pavannaik2004/Beekeeping-DTL/06-digital-twin/exports/step/super_wall_right.step

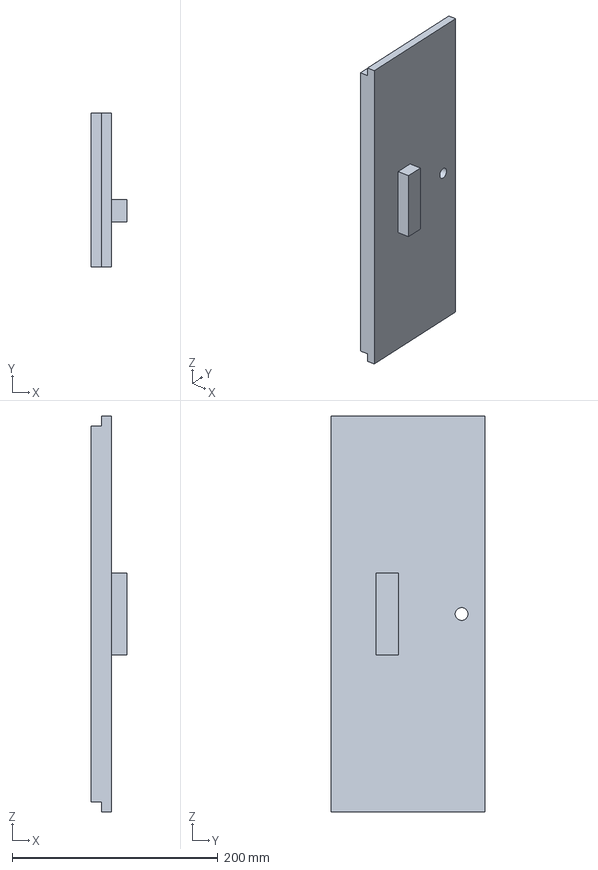
[picture p82: CAD file, 2026-07-14]
06-digital-twin/exports/step/super_wall_right.step
35.0 x 150.0 x 384.6 mm
