pavannaik2004/Beekeeping-DTL/06-digital-twin/exports/step/collection_jar.step

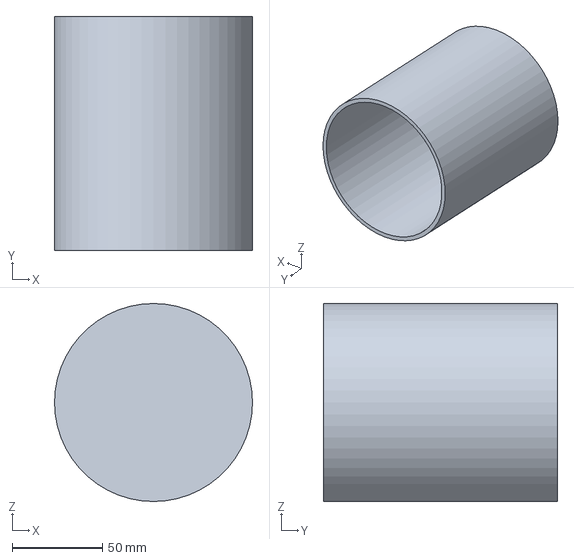
[picture p84: CAD file, 2026-07-14]
06-digital-twin/exports/step/collection_jar.step
110.0 x 130.0 x 110.0 mm
