pavannaik2004/Beekeeping-DTL/06-digital-twin/exports/step/acrylic_left.step

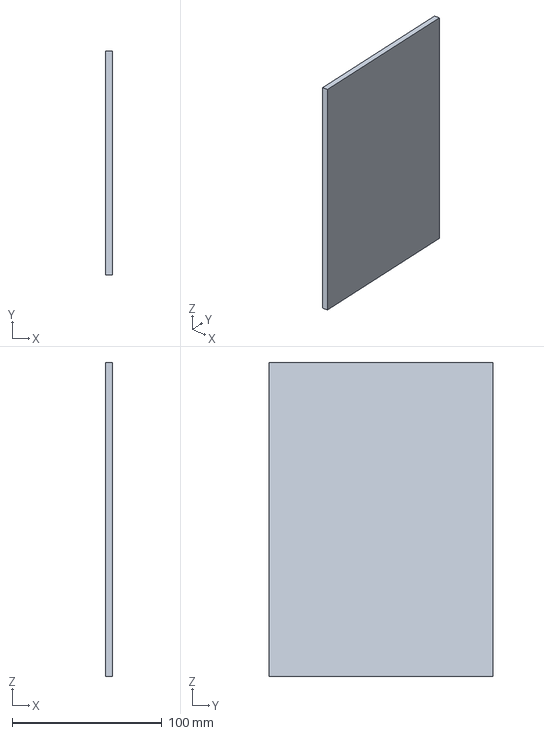
[picture p85: CAD file, 2026-07-14]
06-digital-twin/exports/step/acrylic_left.step
5.00 x 149.8 x 209.8 mm
