pavannaik2004/Beekeeping-DTL/06-digital-twin/exports/step/ff3_fixed.step

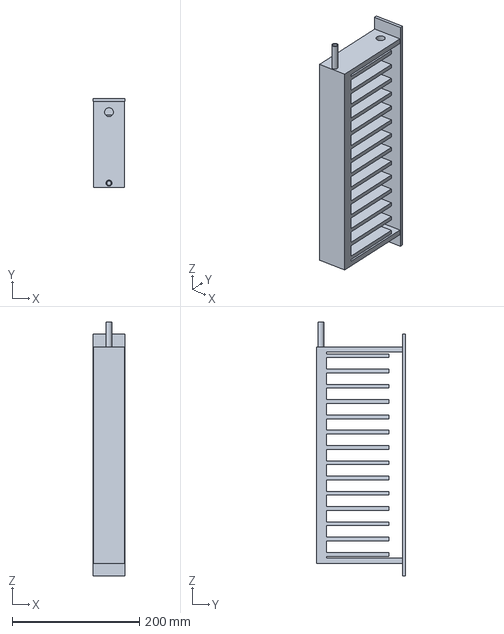
[picture p86: CAD file, 2026-07-14]
06-digital-twin/exports/step/ff3_fixed.step
49.8 x 140.0 x 399.0 mm
