pavannaik2004/Beekeeping-DTL/06-digital-twin/exports/step/acrylic_back.step

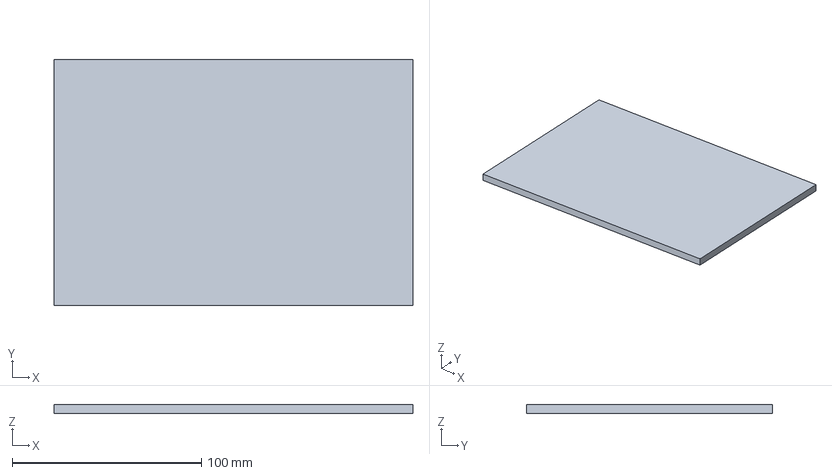
[picture p87: CAD file, 2026-07-14]
06-digital-twin/exports/step/acrylic_back.step
189.8 x 129.8 x 5.00 mm
