pavannaik2004/Beekeeping-DTL/06-digital-twin/exports/step/inner_cover.step

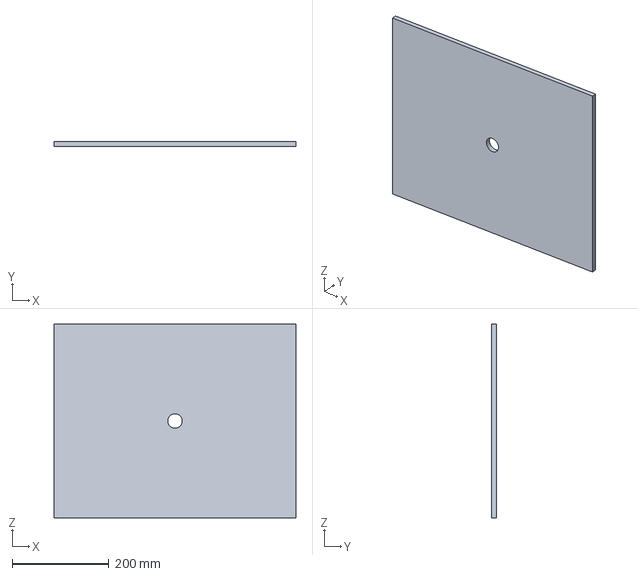
[picture p88: CAD file, 2026-07-14]
06-digital-twin/exports/step/inner_cover.step
501.0 x 10.0 x 401.0 mm
