pavannaik2004/Beekeeping-DTL/06-digital-twin/exports/step/insulation_back.step

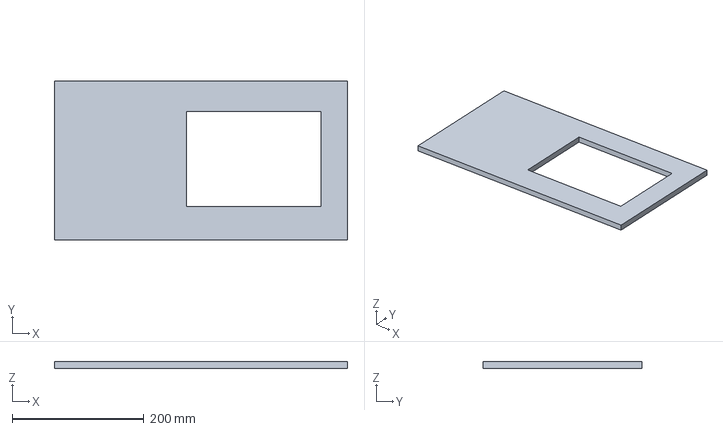
[picture p89: CAD file, 2026-07-14]
06-digital-twin/exports/step/insulation_back.step
445.0 x 241.0 x 10.0 mm
