pavannaik2004/Beekeeping-DTL/06-digital-twin/exports/step/manifold.step

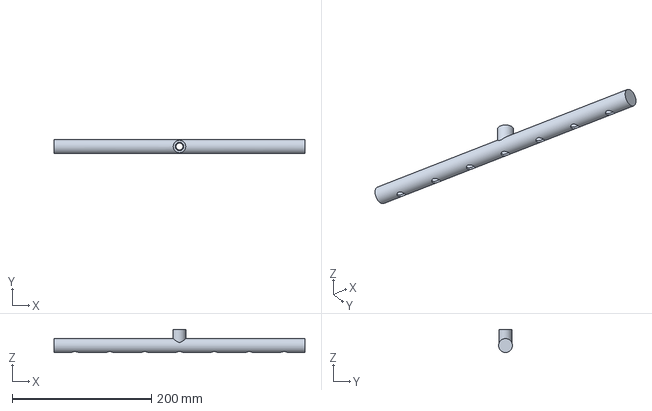
[picture p90: CAD file, 2026-07-14]
06-digital-twin/exports/step/manifold.step
360.0 x 20.0 x 33.0 mm
