pavannaik2004/Beekeeping-DTL/06-digital-twin/exports/step/feeder_tray.step

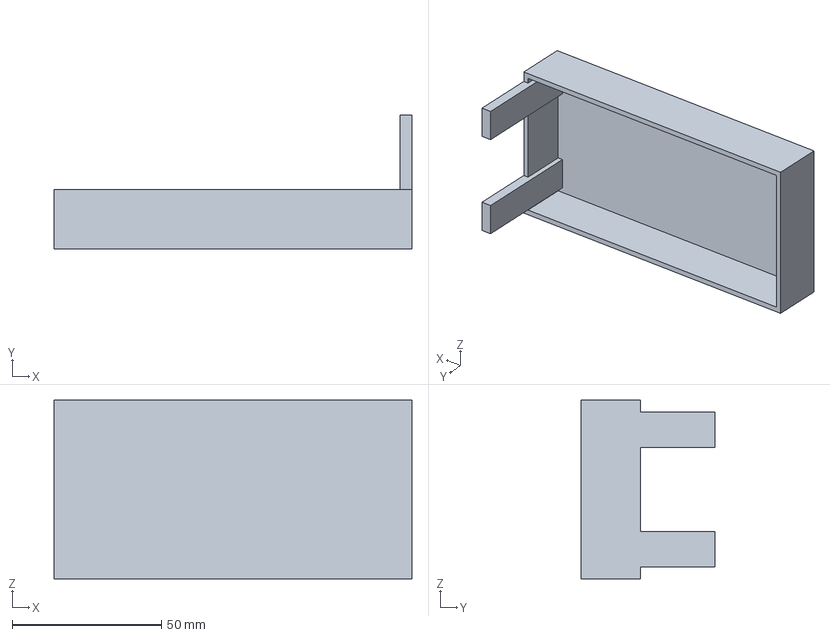
[picture p91: CAD file, 2026-07-14]
06-digital-twin/exports/step/feeder_tray.step
120.0 x 45.0 x 60.0 mm
