pavannaik2004/Beekeeping-DTL/06-digital-twin/exports/step/window_frame_back.step

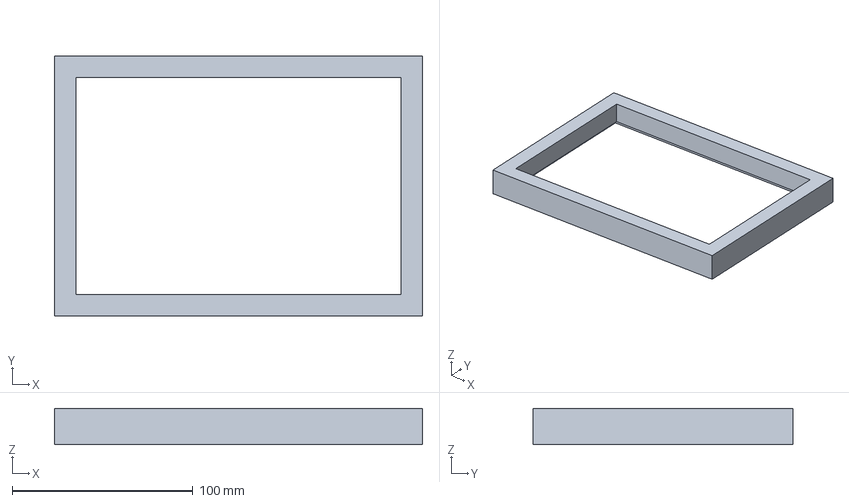
[picture p92: CAD file, 2026-07-14]
06-digital-twin/exports/step/window_frame_back.step
203.8 x 143.8 x 20.0 mm
