pavannaik2004/Beekeeping-DTL/06-digital-twin/exports/step/shutter_left.step

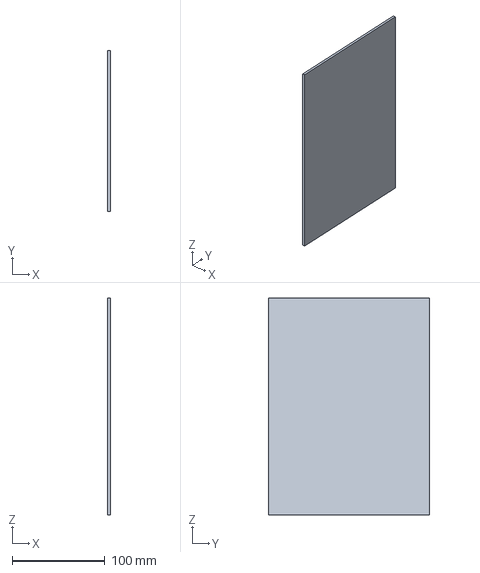
[picture p93: CAD file, 2026-07-14]
06-digital-twin/exports/step/shutter_left.step
3.00 x 174.0 x 234.0 mm
