pavannaik2004/Beekeeping-DTL/06-digital-twin/exports/step/water_ring.step

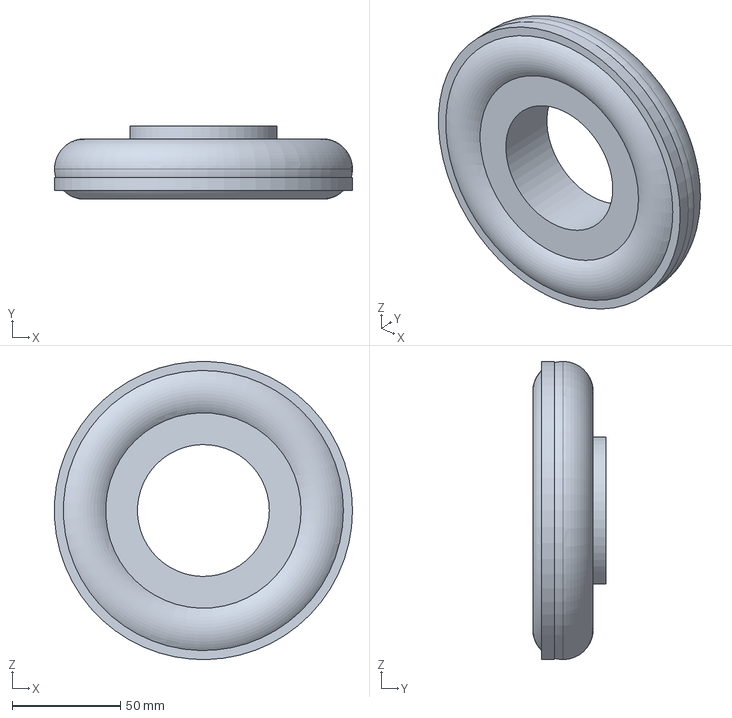
[picture p94: CAD file, 2026-07-14]
06-digital-twin/exports/step/water_ring.step
137.9 x 34.0 x 137.9 mm
