pavannaik2004/Beekeeping-DTL/06-digital-twin/exports/step/stand_foot.step

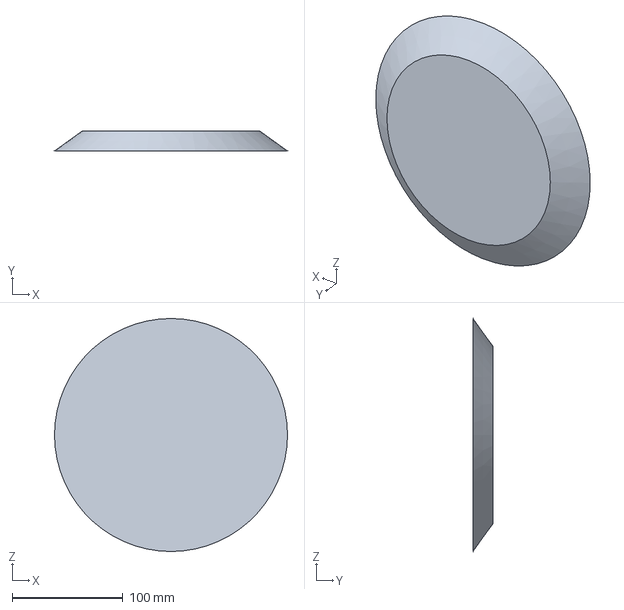
[picture p95: CAD file, 2026-07-14]
06-digital-twin/exports/step/stand_foot.step
210.0 x 18.0 x 210.0 mm
