pavannaik2004/Beekeeping-DTL/06-digital-twin/exports/step/floor_board.step

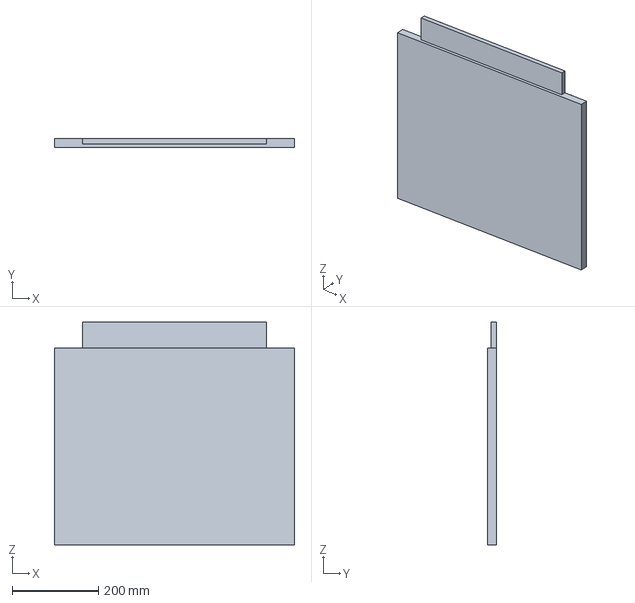
[picture p96: CAD file, 2026-07-14]
06-digital-twin/exports/step/floor_board.step
555.0 x 20.0 x 515.0 mm
