pavannaik2004/Beekeeping-DTL/06-digital-twin/exports/step/brood_wall_front.step

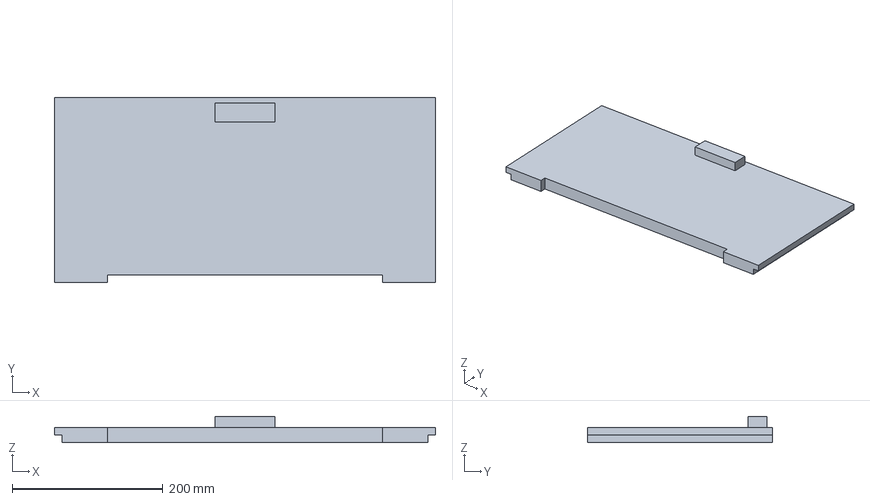
[picture p97: CAD file, 2026-07-14]
06-digital-twin/exports/step/brood_wall_front.step
505.0 x 245.0 x 35.0 mm
