pavannaik2004/Beekeeping-DTL/06-digital-twin/exports/step/insulation_left.step

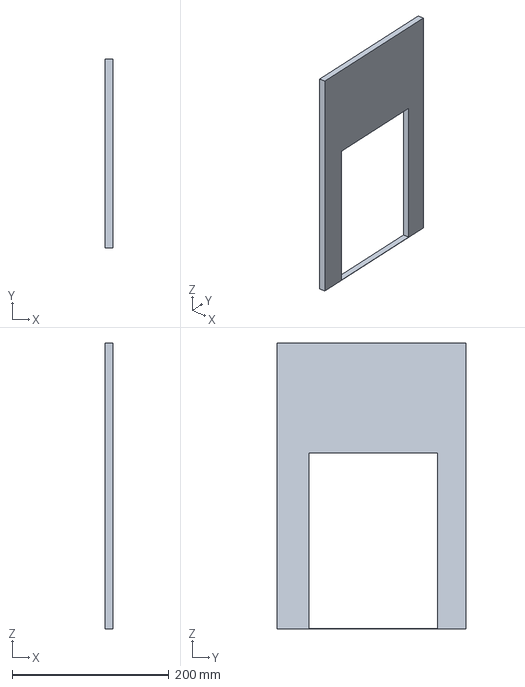
[picture p99: CAD file, 2026-07-14]
06-digital-twin/exports/step/insulation_left.step
10.0 x 241.0 x 365.0 mm
