pavannaik2004/Beekeeping-DTL/06-digital-twin/exports/step/insulation_right.step

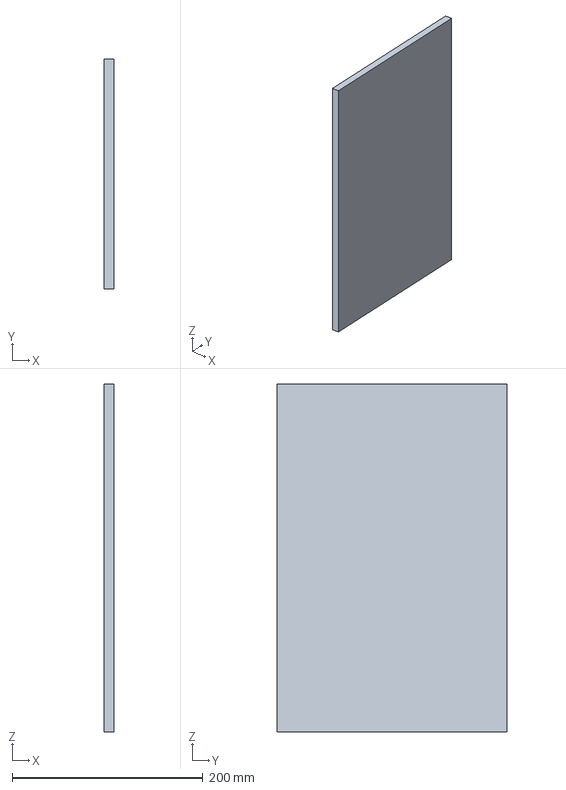
[picture p100: CAD file, 2026-07-14]
06-digital-twin/exports/step/insulation_right.step
10.0 x 241.0 x 365.0 mm
