pavannaik2004/Beekeeping-DTL/06-digital-twin/exports/step/window_frame_left.step

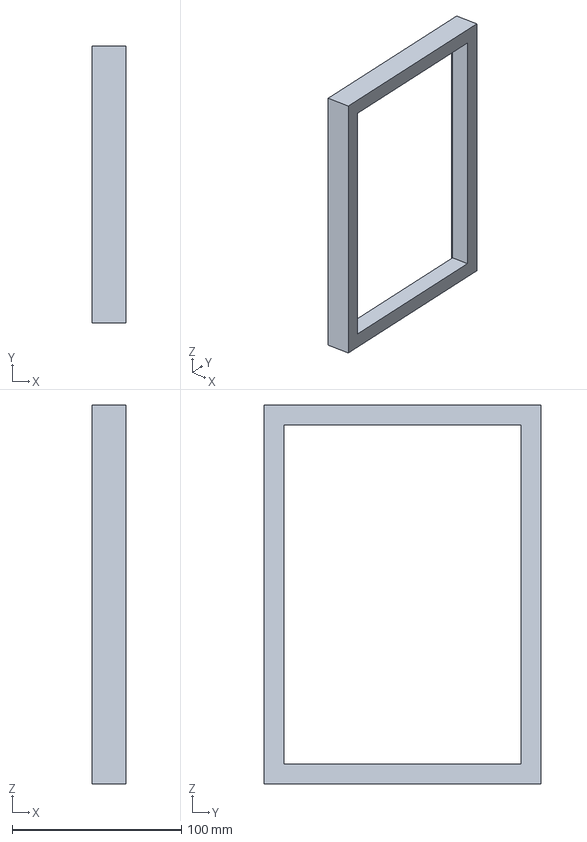
[picture p101: CAD file, 2026-07-14]
06-digital-twin/exports/step/window_frame_left.step
20.0 x 163.8 x 223.8 mm
