pavannaik2004/Beekeeping-DTL/06-digital-twin/exports/step/brood_wall_left.step

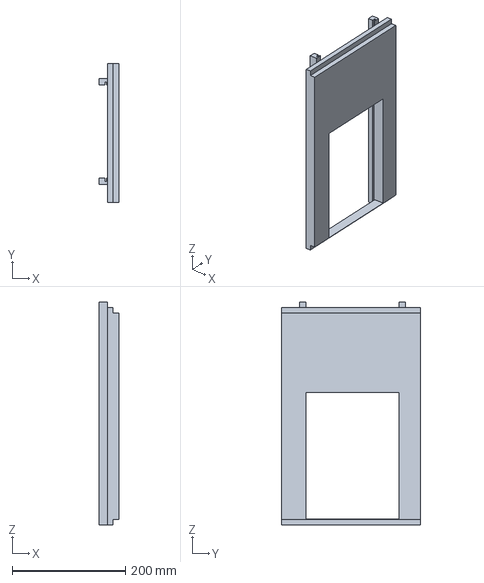
[picture p102: CAD file, 2026-07-14]
06-digital-twin/exports/step/brood_wall_left.step
35.0 x 245.0 x 394.3 mm
